TrimVa/trimbox_v2/trimbox_s3/src/console_gz.h

// FICHIER GÉNÉRÉ par tools/embed_console.py — NE PAS MODIFIER À LA MAIN.
// Source : index.html, console v1.7.18, 200560 octets (sha1 fe6caef0e6d3),
// compressée en 64454 octets.
#pragma once
#include <stdint.h>
#include <stddef.h>
#define CONSOLE_EMBED_VER "1.7.18"
static const size_t CONSOLE_GZ_LEN = 64454;
static const uint8_t CONSOLE_GZ[] = {
  0x1F,0x8B,0x08,0x00,0x00,0x00,0x00,0x00,0x02,0xFF,0xEC,0xBD,0xD9,0x6E,0x23,0xC9,0x96,0x20,0xF8,0x1E,
  0x5F,0x61,0xA9,0xCC,0x2C,0x92,0x19,0x24,0x45,0x52,0xA2,0x42,0xA2,0x42,0xCA,0xD6,0x1A,0xA1,0xB8,0x5A,
  0x22,0xB5,0xC6,0x52,0x81,0x4C,0x27,0xDD,0x48,0xBA,0xE4,0x74,0x67,0xBA,0x3B,0xB5,0x84,0xAE,0x80,0xFB,
  0x34,0xE8,0xFB,0x34,0x85,0x46,0xA3,0x1B,0x98,0xA7,0x3B,0x0F,0x53,0x55,0x51,0x05,0xCC,0x02,0x14,0x30,
  0x33,0x28,0x60,0x1E,0x52,0x7F,0x72,0xBF,0xA4,0xCF,0x62,0xE6,0x6E,0xEE,0x74,0x4A,0x8C,0xCC,0x48,0x74,
  0x0F,0x70,0x23,0x91,0x11,0x74,0x77,0xB3,0x63,0x66,0xC7,0x8E,0x9D,0xCD,0x8E,0x1D,0x7B,0xFE,0xD5,0xE6,
  0xC1,0xC6,0xF1,0xDB,0xD7,0x5B,0xA2,0x1F,0x0D,0xDC,0xD5,0x27,0xCF,0xF1,0x1F,0xE1,0x5A,0x5E,0x6F,0x65,
  0xA6,0x1B,0xCC,0xE0,0x0B,0x69,0xD9,0xF0,0xCF,0x40,0x46,0x96,0xE8,0xF4,0xAD,0x20,0x94,0xD1,0xCA,0xCC,
  0x28,0xEA,0x56,0x16,0x67,0xF4,0x6B,0xCF,0x1A,0xC8,0x95,0x99,0x4B,0x47,0x5E,0x0D,0xFD,0x20,0x9A,0x11,
  0x1D,0xDF,0x8B,0xA4,0x07,0xC5,0xAE,0x1C,0x3B,0xEA,0xAF,0xD8,0xF2,0xD2,0xE9,0xC8,0x0A,0x3D,0x94,0x85,
  0xE3,0x39,0x91,0x63,0xB9,0x95,0xB0,0x63,0xB9,0x72,0xA5,0x5E,0x16,0xBA,0x5E,0xA5,0xEB,0x44,0x2B,0x1D,
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
  0x76,0x8F,0xD6,0xAF,0xAC,0xB3,0xEB,0x4B,0xFB,0xC5,0xB6,0x07,0x70,0x36,0xDA,0x2F,0x4F,0x5D,0xFB,0xC5,
  0x12,0x3C,0xF7,0x7A,0xEF,0xDE,0xFC,0xD0,0x7B,0x7B,0xD6,0xEC,0xB7,0x5F,0xBA,0x1F,0x55,0x3B,0x1F,0xDF,
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
};
